iot-kits/D1S-Display-WBIT/images/Figure 3 - D1 placed.png

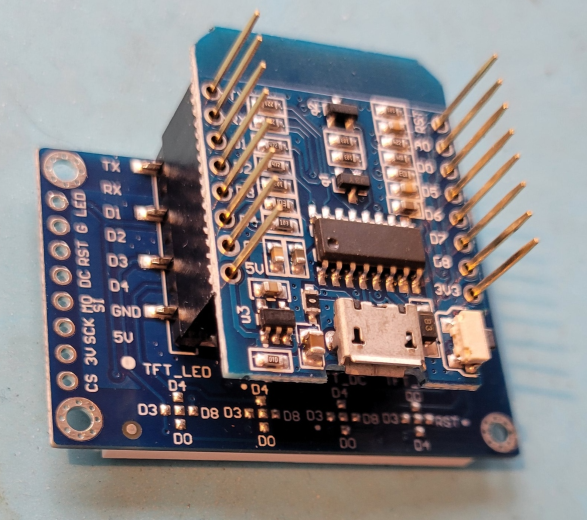
images/Figure 3 - D1 placed.png
