iot-kits/D1S-Display-WBIT/ota.h

// !!!DO NOT CHANGE!!!
//! PlatformIO format
const String fwURLbase    = "https://w4krl.com/fota/";
const String fwPath       = FW_FILENAME + "/";
const String fwVersionURL = fwURLbase + fwPath + "version.h";
const String fwImageURL   = fwURLbase + fwPath + "firmware.bin";
